Dmm0777/eq-circuit-project/simulations/eqsim.asc

C1: cap; 470nF
C2: cap; 680n
C3: cap; 68n
C4: cap; 68nF
C5: cap; 6.8nF
C6: cap; 6.8nF
C7: cap; 680pF
C8: cap; 10µ
C9: cap; 10µ
C10: cap; 10µ
C11: cap; 10µ
C12: cap; 10µ
C13: cap; 10µ
C14: cap; 10µ
C15: cap; 10µ
C16: cap; 10µ
C17: cap; 10µ
I1: current; ""; AC 1
R1: res; 3.3k
R2: res; 980
R3: res; 1k
R4: res; 20
R5: res; 68k
R6: res; 47k
R7: res; 68k
R8: res; 1k
R9: res; 1k
R10: res; 68k
R11: res; 3.3k
U1: UniversalOpAmp1
U2: UniversalOpAmp1
U3: UniversalOpAmp1
U4: UniversalOpAmp1
U5: UniversalOpAmp1
V1: voltage; 12
V2: voltage; 12
VR1.1: res; 20
VR1.2: res; 980
VR2.1: res; 20
VR2.2: res; 980
Named nets: 0, OUT, +12V, -12V
.ac lin 100000 10 20k
