Dmm0777/eq-circuit-project/schematics/eq1 - Copy.kicad_sch

## KiCad design schematics/eq1 - Copy.kicad_sch (2026-03-31)

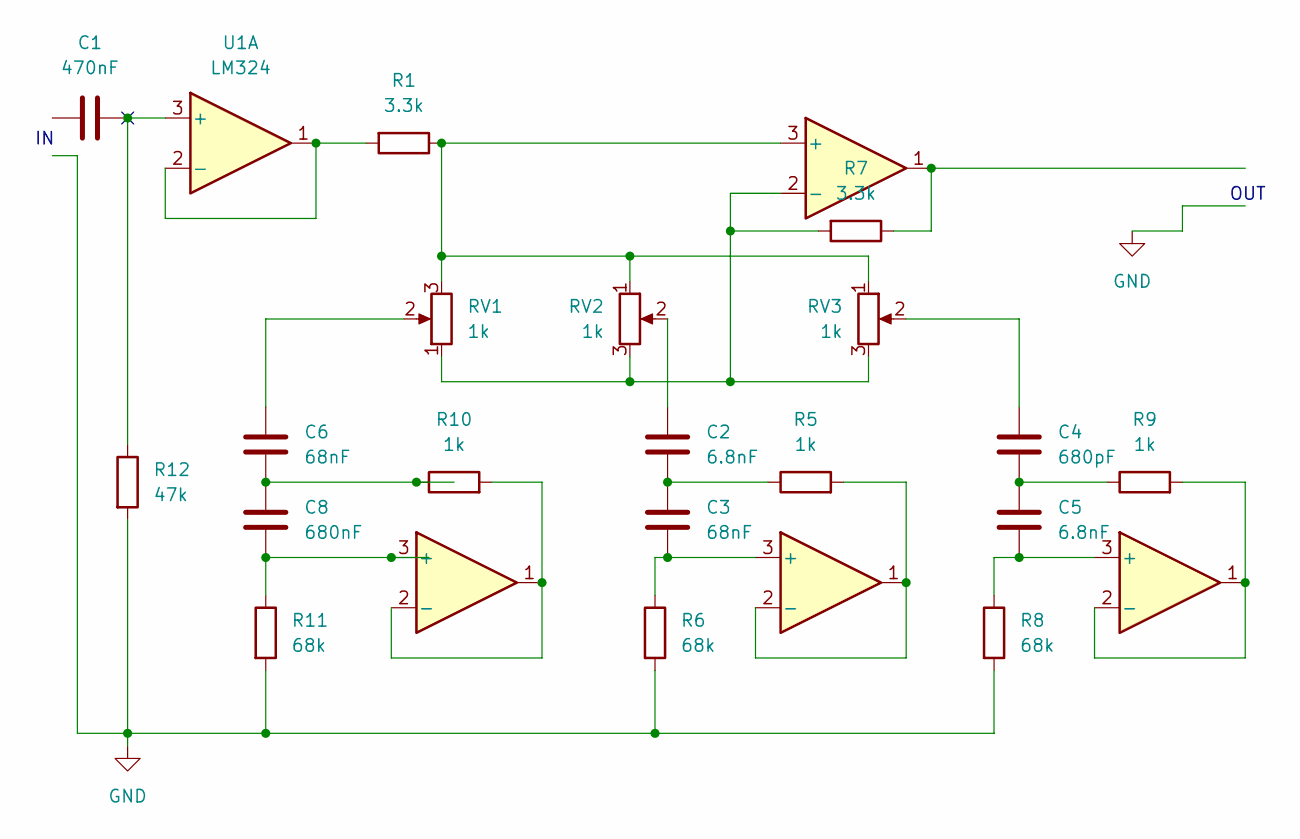
[picture p5: schematic eq1 - Copy.kicad_sch]

Parts:
C1: 470nF
C2, C5: 6.8nF
C3, C6: 68nF
C4: 680pF
C8: 680nF
R1, R7: 3.3k
R5, R9, R10: 1k
R6, R8, R11: 68k
R12: 47k
RV1, RV2, RV3: 1k
U1, U2, U3, U4, U5: LM324

Connections:
GND: R6.2, R8.2, R11.2, R12.2
unnamed: C1.1, R12.1, U1.3 (+)
unnamed: C2.1, RV2.2
unnamed: C2.2, C3.1, R5.1
unnamed: C3.2, R6.1, U2.3 (+)
unnamed: C4.1, RV3.2
unnamed: C4.2, C5.1, R9.1
unnamed: C5.2, R8.1, U4.3 (+)
unnamed: C6.1, RV1.2
unnamed: C6.2, C8.1, R10.1
unnamed: C8.2, R11.1, U5.3 (+)
unnamed: R1.1, RV1.3, RV2.1, RV3.1, U3.3 (+)
unnamed: R1.2, U1.1, U1.2 (-)
unnamed: R5.2, U2.1, U2.2 (-)
unnamed: R7.1, U3.1
unnamed: R7.2, RV1.1, RV2.3, RV3.3, U3.2 (-)
unnamed: R9.2, U4.1, U4.2 (-)
unnamed: R10.2, U5.1, U5.2 (-)

Notes on the sheet:
OUT
